hydra-eng/CryoSentinel/hardware/cryosentinel.kicad_sch

## KiCad design hardware/cryosentinel.kicad_sch (2026-06-14, an earlier design)

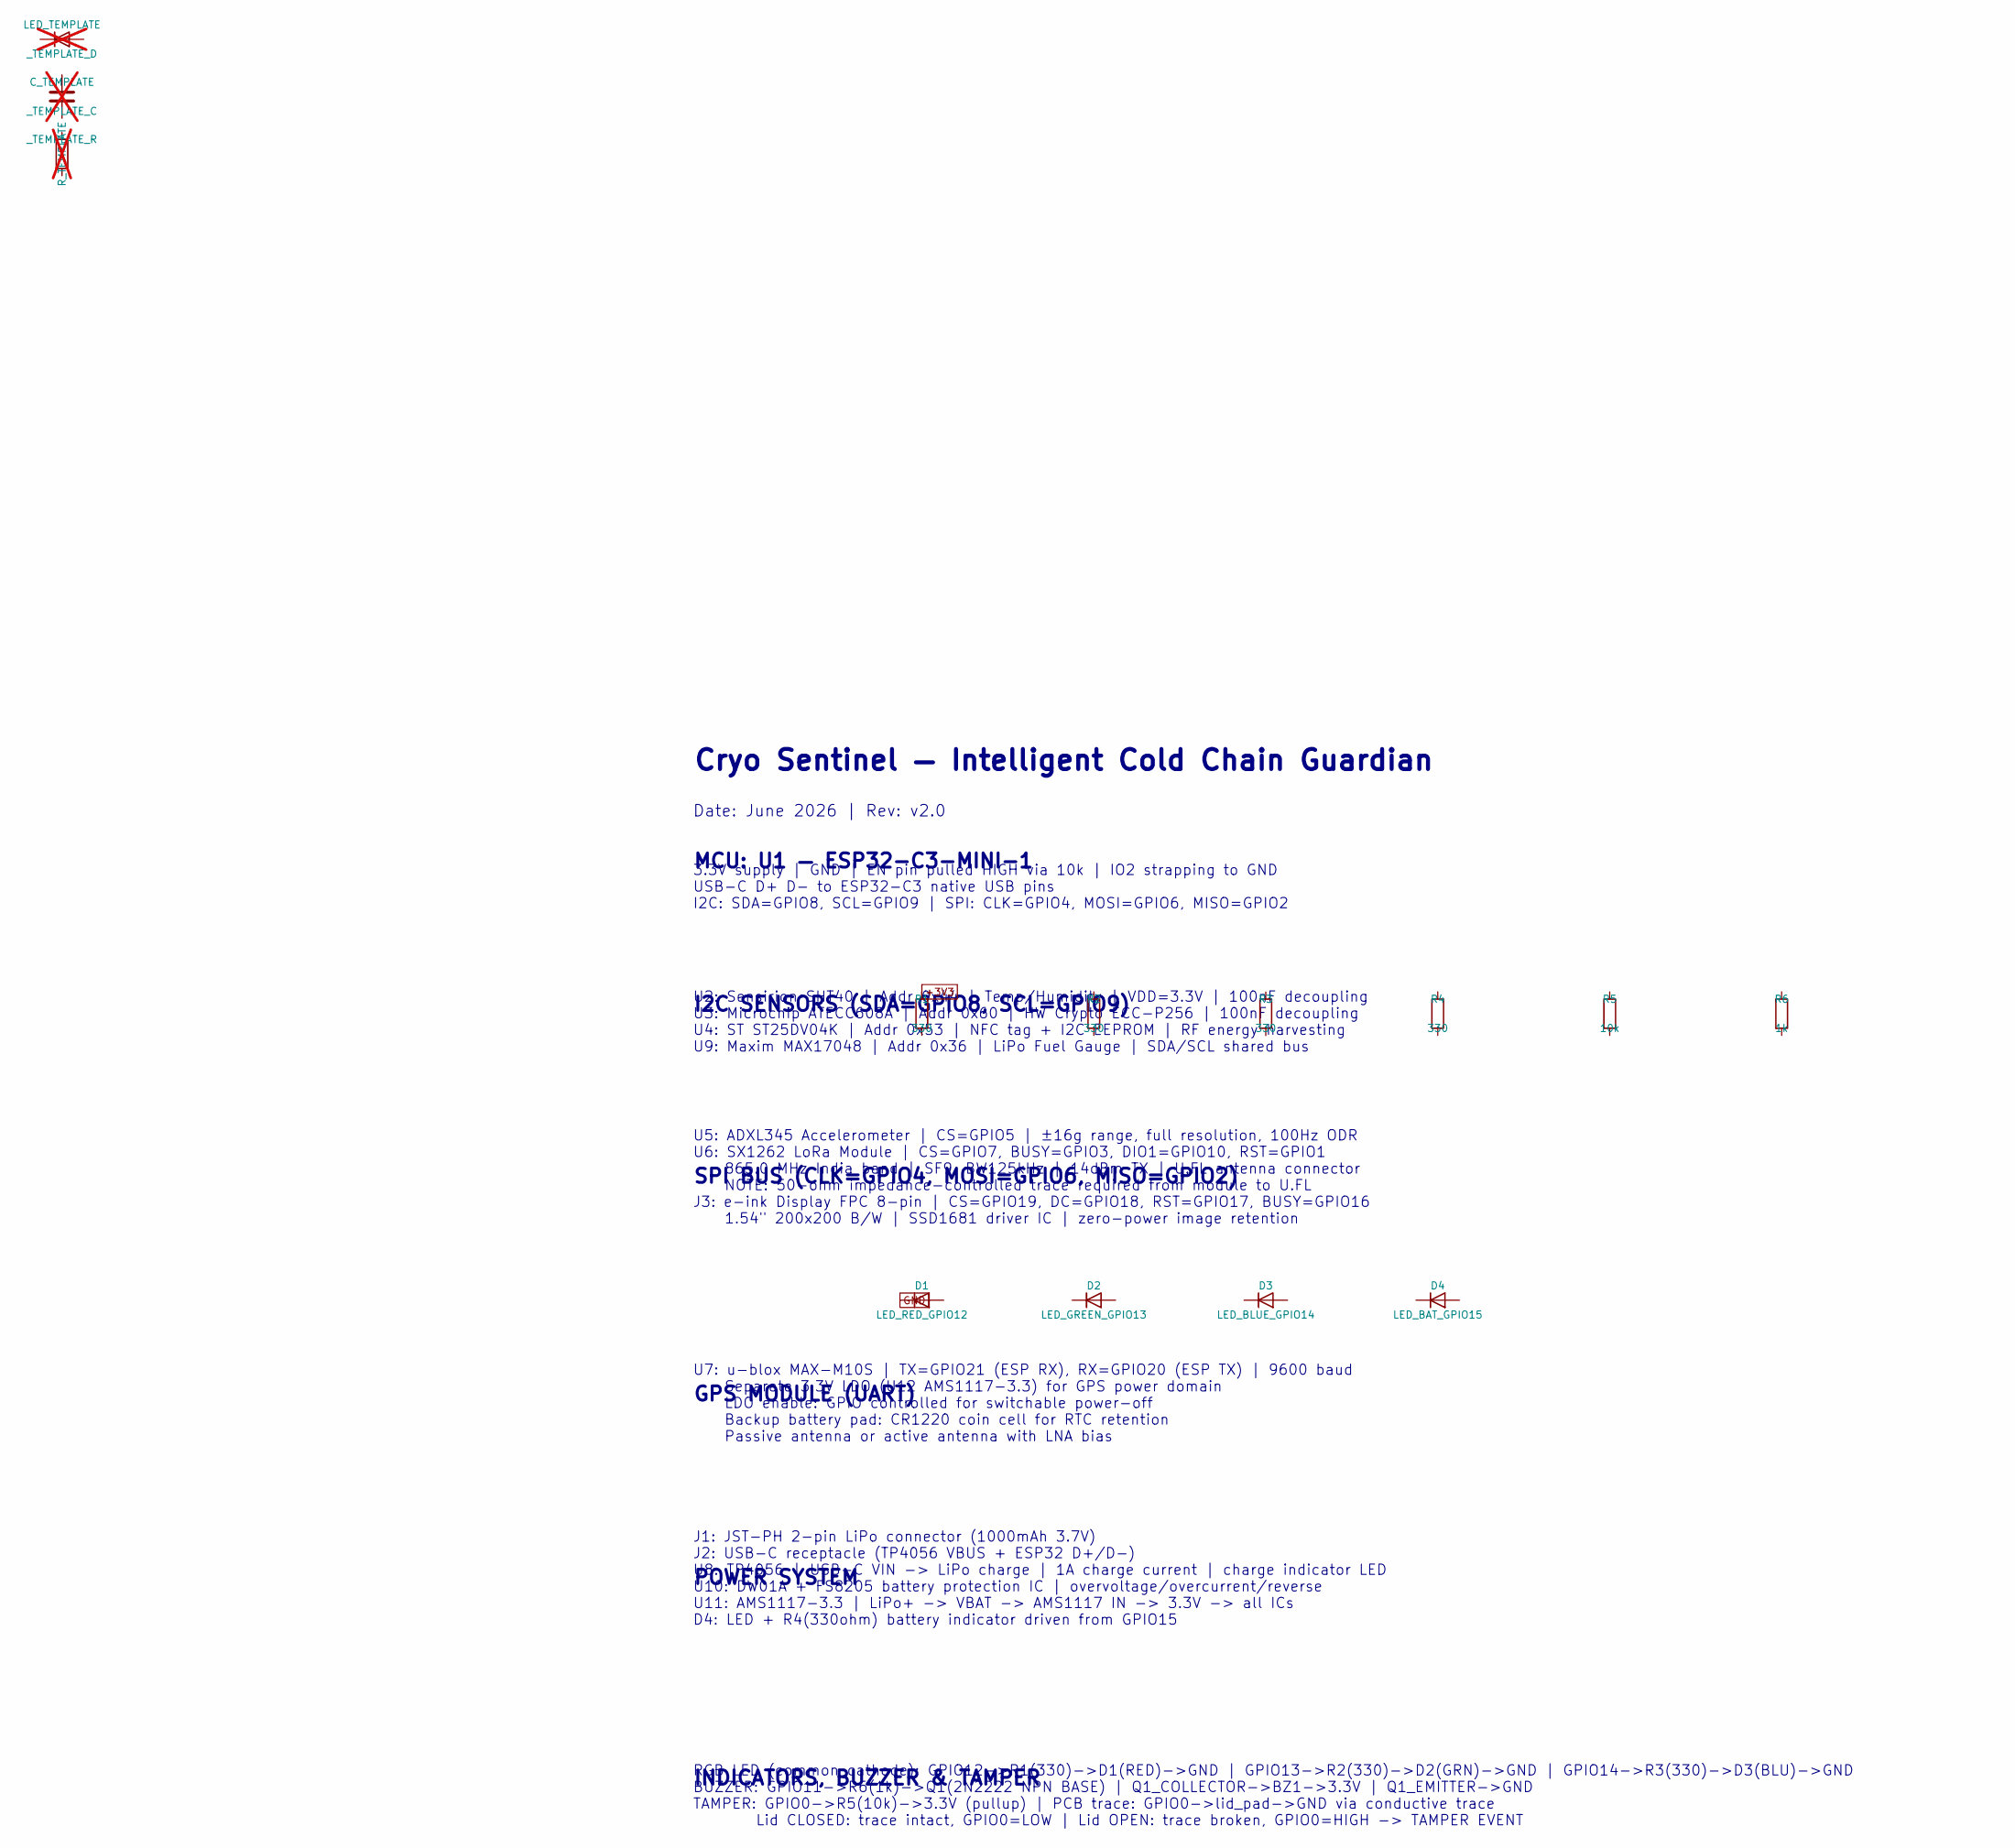
[picture p12: schematic cryosentinel.kicad_sch]

Parts:
D1: LED_RED_GPIO12; LED_0603_1608Metric
D2: LED_GREEN_GPIO13; LED_0603_1608Metric
D3: LED_BLUE_GPIO14; LED_0603_1608Metric
D4: LED_BAT_GPIO15; LED_0603_1608Metric
R1, R2, R3, R4: 330; R_0603_1608Metric
R5: 10k; R_0603_1608Metric
R6: 1k; R_0603_1608Metric
_TEMPLATE_C: C_TEMPLATE; not fitted
_TEMPLATE_D: LED_TEMPLATE; not fitted
_TEMPLATE_R: R_TEMPLATE; not fitted

Connections:
+3V3: R1.1
GND: D1.1 (K)

Notes on the sheet:
Cryo Sentinel — Intelligent Cold Chain Guardian
Date: June 2026 | Rev: v2.0
MCU: U1 — ESP32-C3-MINI-1
3.3V supply | GND | EN pin pulled HIGH via 10k | IO2 strapping to GND USB-C D+ D- to ESP32-C3 native USB pins I2C: SDA=GPIO8, SCL=GPIO9 | SPI: CLK=GPIO4, MOSI=GPIO6, MISO=GPIO2
I2C SENSORS (SDA=GPIO8, SCL=GPIO9)
U2: Sensirion SHT40 | Addr 0x44 | Temp/Humidity | VDD=3.3V | 100nF decoupling U3: Microchip ATECC608A | Addr 0x60 | HW Crypto ECC-P256 | 100nF decoupling U4: ST ST25DV04K | Addr 0x53 | NFC tag + I2C EEPROM | RF energy harvesting U9: Maxim MAX17048 | Addr 0x36 | LiPo Fuel Gauge | SDA/SCL shared bus
SPI BUS (CLK=GPIO4, MOSI=GPIO6, MISO=GPIO2)
U5: ADXL345 Accelerometer | CS=GPIO5 | ±16g range, full resolution, 100Hz ODR U6: SX1262 LoRa Module | CS=GPIO7, BUSY=GPIO3, DIO1=GPIO10, RST=GPIO1 865.0 MHz India band | SF9, BW125kHz | 14dBm TX | U.FL antenna connector NOTE: 50-ohm impedance-controlled trace required from module to U.FL J3: e-ink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
GPS MODULE (UART)
U7: u-blox MAX-M10S | TX=GPIO21 (ESP RX), RX=GPIO20 (ESP TX) | 9600 baud Separate 3.3V LDO (U12 AMS1117-3.3) for GPS power domain LDO enable: GPIO controlled for switchable power-off Backup battery pad: CR1220 coin cell for RTC retention Passive antenna or active antenna with LNA bias
POWER SYSTEM
J1: JST-PH 2-pin LiPo connector (1000mAh 3.7V) J2: USB-C receptacle (TP4056 VBUS + ESP32 D+/D-) U8: TP4056 | USB-C VIN -> LiPo charge | 1A charge current | charge indicator LED U10: DW01A + FS8205 battery protection IC | overvoltage/overcurrent/reverse U11: AMS1117-3.3 | LiPo+ -> VBAT -> AMS1117 IN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
INDICATORS, BUZZER & TAMPER
RGB LED (common cathode): GPIO12->R1(330)->D1(RED)->GND | GPIO13->R2(330)->D2(GRN)->GND | GPIO14->R3(330)->D3(BLU)->GND BUZZER: GPIO11->R6(1k)->Q1(2N2222 NPN BASE) | Q1_COLLECTOR->BZ1->3.3V | Q1_EMITTER->GND TAMPER: GPIO0->R5(10k)->3.3V (pullup) | PCB trace: GPIO0->lid_pad->GND via conductive trace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
